BrandenburgTech/DigitalTxRxRPi/afsktx/main.c

/*
 *  A sample application transmitting AFSK at 1200 baud
 *
 *  Portions Copyright (C) 2018 Jonathan Brandenburg
 *
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
 *  You should have received a copy of the GNU General Public License
 *  along with this program.  If not, see <http://www.gnu.org/licenses/>.
 */

#include <stdlib.h>
#include <stdio.h>
#include <unistd.h>
#include <string.h>
#include "status.h"
#include "ax5043.h"
#include "ax25.h"
#include "spi/ax5043spi.h"

ax5043_conf_t hax5043;
ax25_conf_t hax25;

static void init_rf();

int main(void) {
    setSpiChannel(SPI_CHANNEL);
    setSpiSpeed(SPI_SPEED);
    initializeSpi();

    init_rf();

    ax25_init(&hax25, (uint8_t *) "CALLXX", '2', (uint8_t *) "CALLXX", '2',
    AX25_PREAMBLE_LEN,
    AX25_POSTAMBLE_LEN);

    int ret;
    uint8_t data[1024];
    // 0x03 is a UI frame
    // 0xF0 is no Level 3 protocol
    const char *str = "\x03\xf0This is an AX.25 Packet!!!";

    /* Infinite loop */
    for (;;) {
        sleep(2);
        printf("INFO: Transmitting a packet\n");

        memcpy(data, str, strnlen(str, 256));
        ret = ax25_tx_frame(&hax25, &hax5043, data, strnlen(str, 256));
        if (ret) {
            fprintf(stderr,
                    "ERROR: Failed to transmit AX.25 frame with error code %d\n",
                    ret);
            exit(EXIT_FAILURE);
        }
        ax5043_wait_for_transmit();
        if (ret) {
            fprintf(stderr,
                    "ERROR: Failed to transmit entire AX.25 frame with error code %d\n",
                    ret);
            exit(EXIT_FAILURE);
        }

    }

    return 0;
}

static void init_rf() {
    int ret;
    ret = ax5043_init(&hax5043, XTAL_FREQ_HZ, VCO_INTERNAL);
    if (ret != PQWS_SUCCESS) {
        fprintf(stderr,
                "ERROR: Failed to initialize AX5043 with error code %d\n", ret);
        exit(EXIT_FAILURE);
    }
}
